gerb-ster/YUSynth-LFO/images/IMG_1308.jpeg

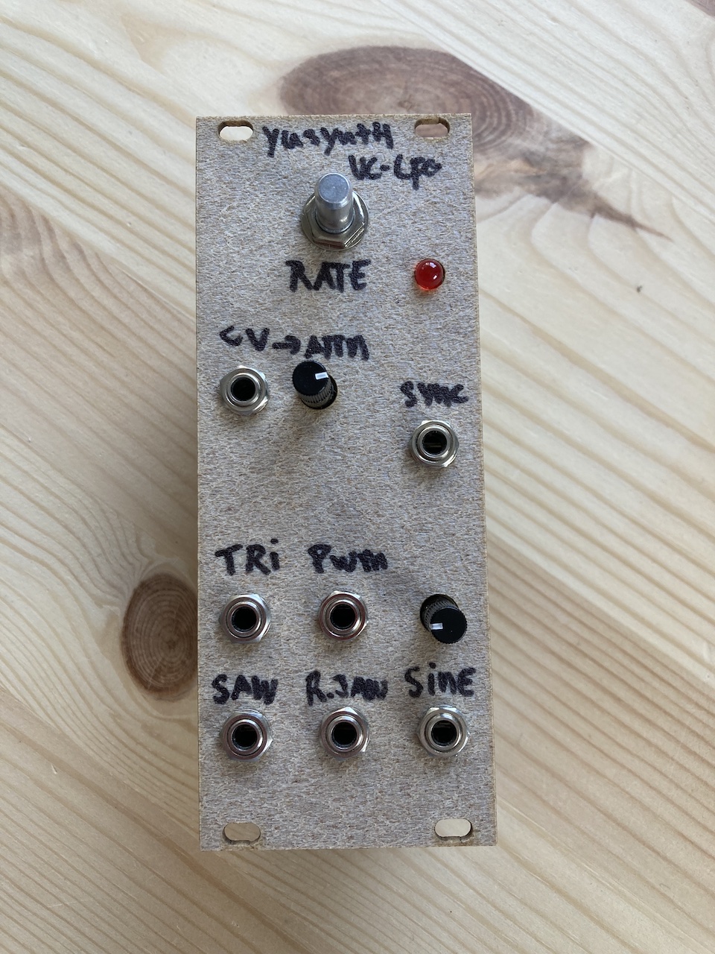
images/IMG_1308.jpeg
