gerb-ster/YUSynth-LFO/images/IMG_1309.jpeg

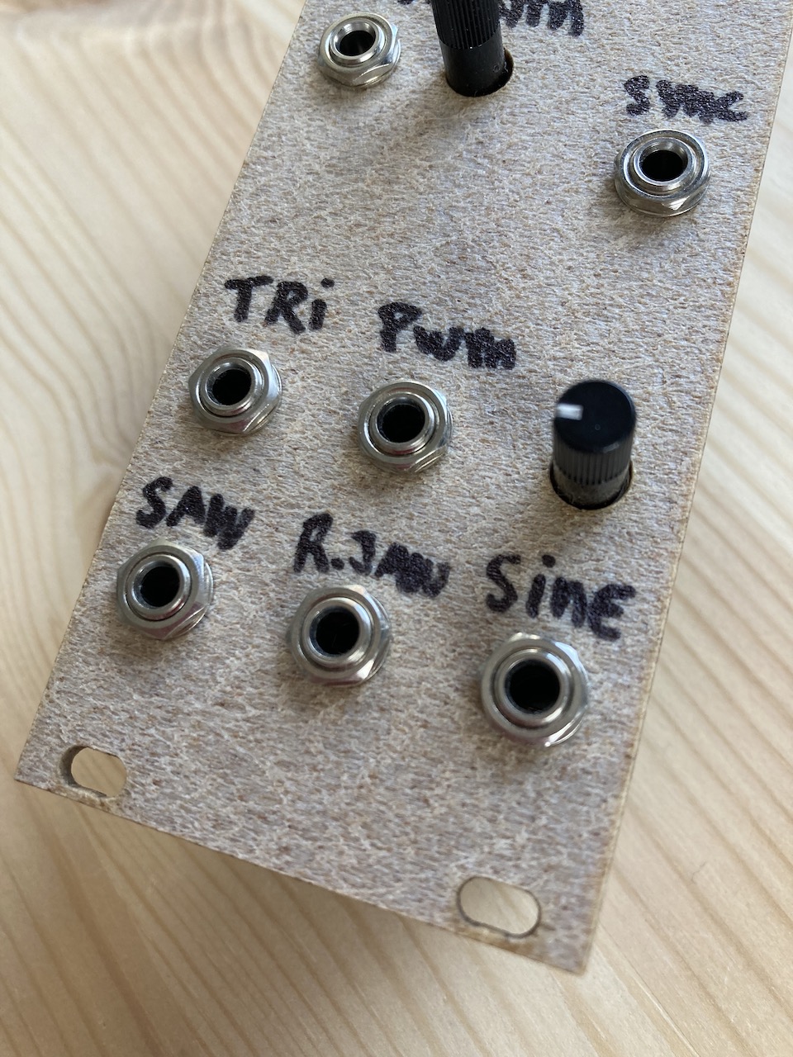
images/IMG_1309.jpeg
