gerb-ster/YUSynth-LFO/images/IMG_1310.jpeg

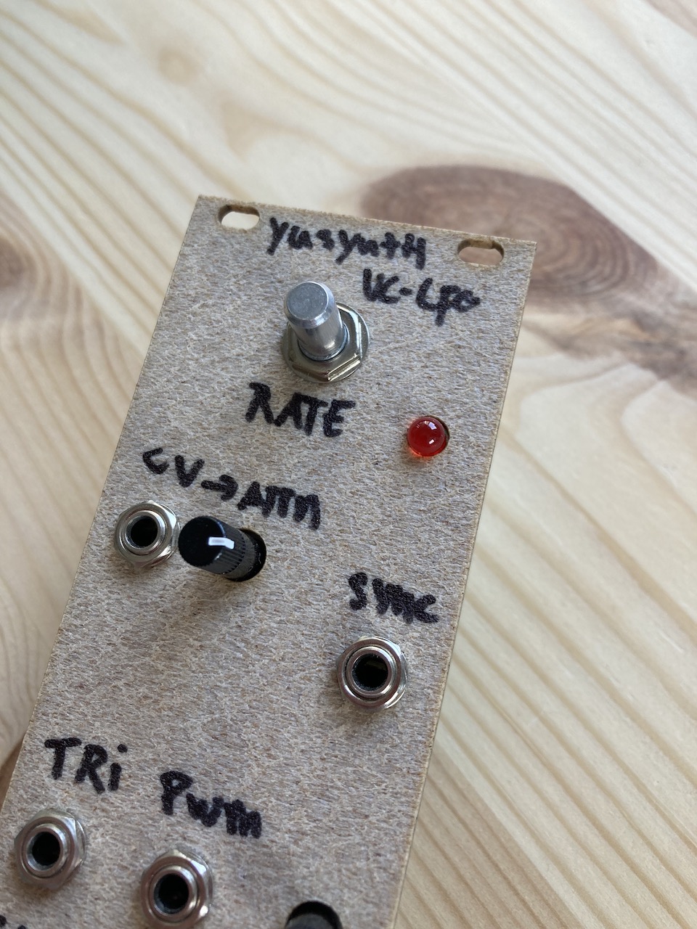
images/IMG_1310.jpeg
