gerb-ster/YUSynth-LFO/images/IMG_1311.jpeg

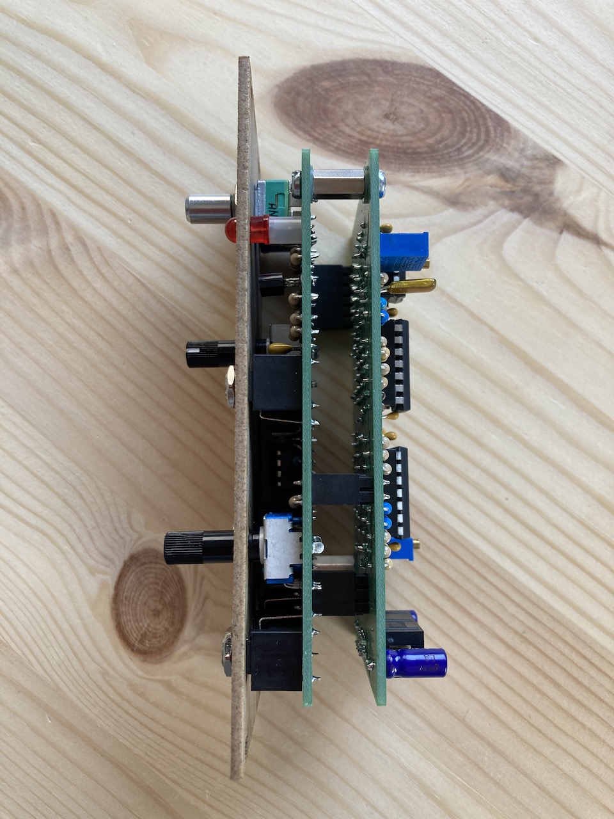
images/IMG_1311.jpeg
