gerb-ster/YUSynth-LFO/images/IMG_1313.jpeg

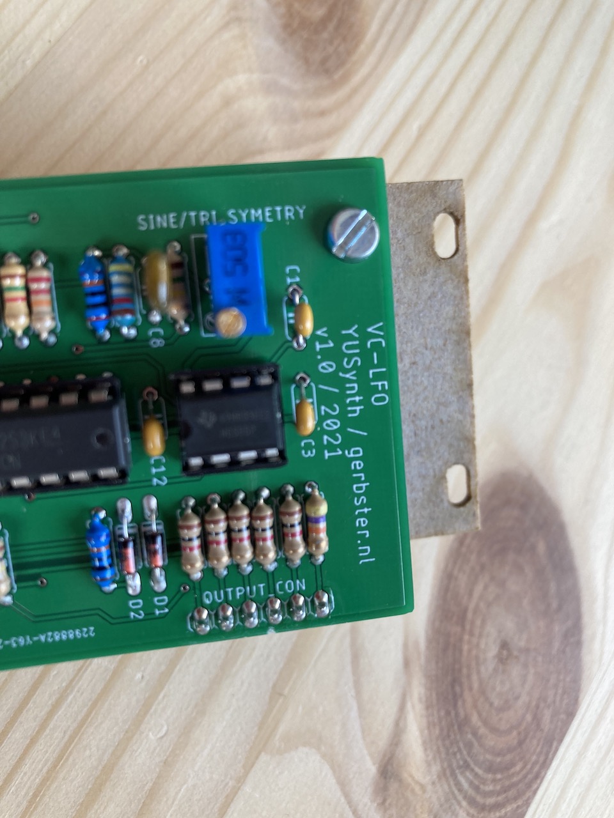
images/IMG_1313.jpeg
