gerb-ster/YUSynth-LFO/images/YUSynth-LFO-ioboard.png

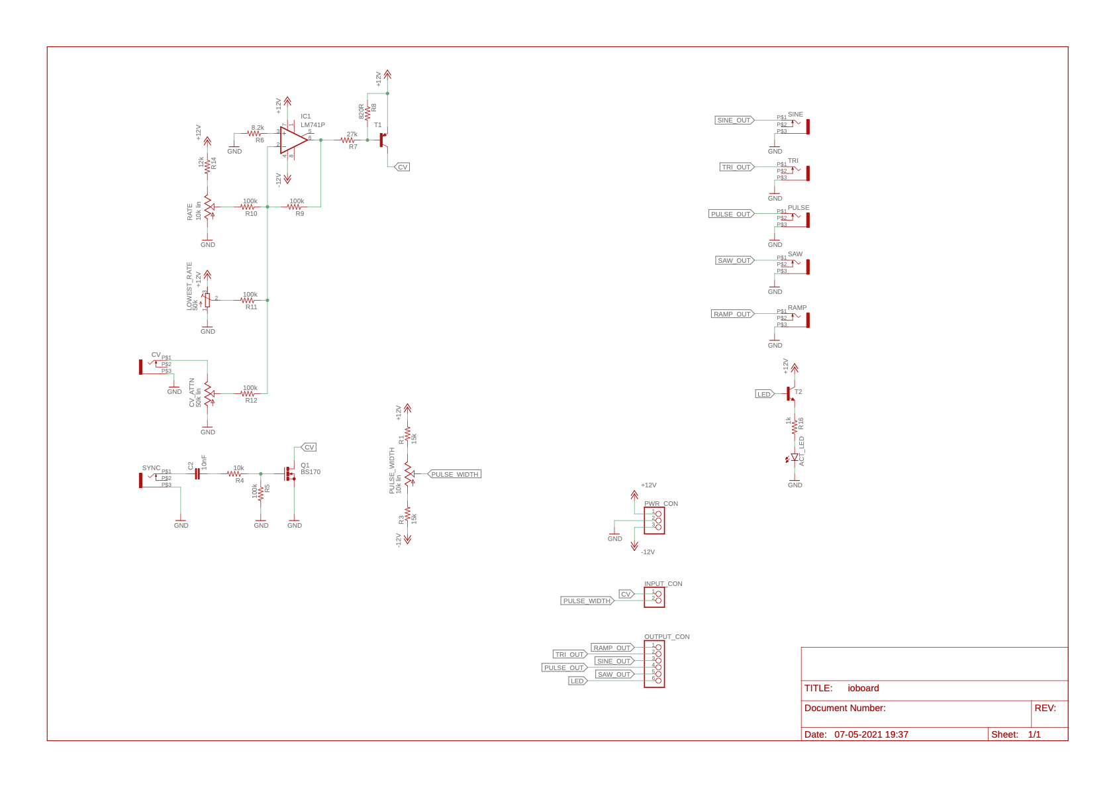
images/YUSynth-LFO-ioboard.png
