gerb-ster/YUSynth-LFO/images/YUSynth-LFO-mainboard.png

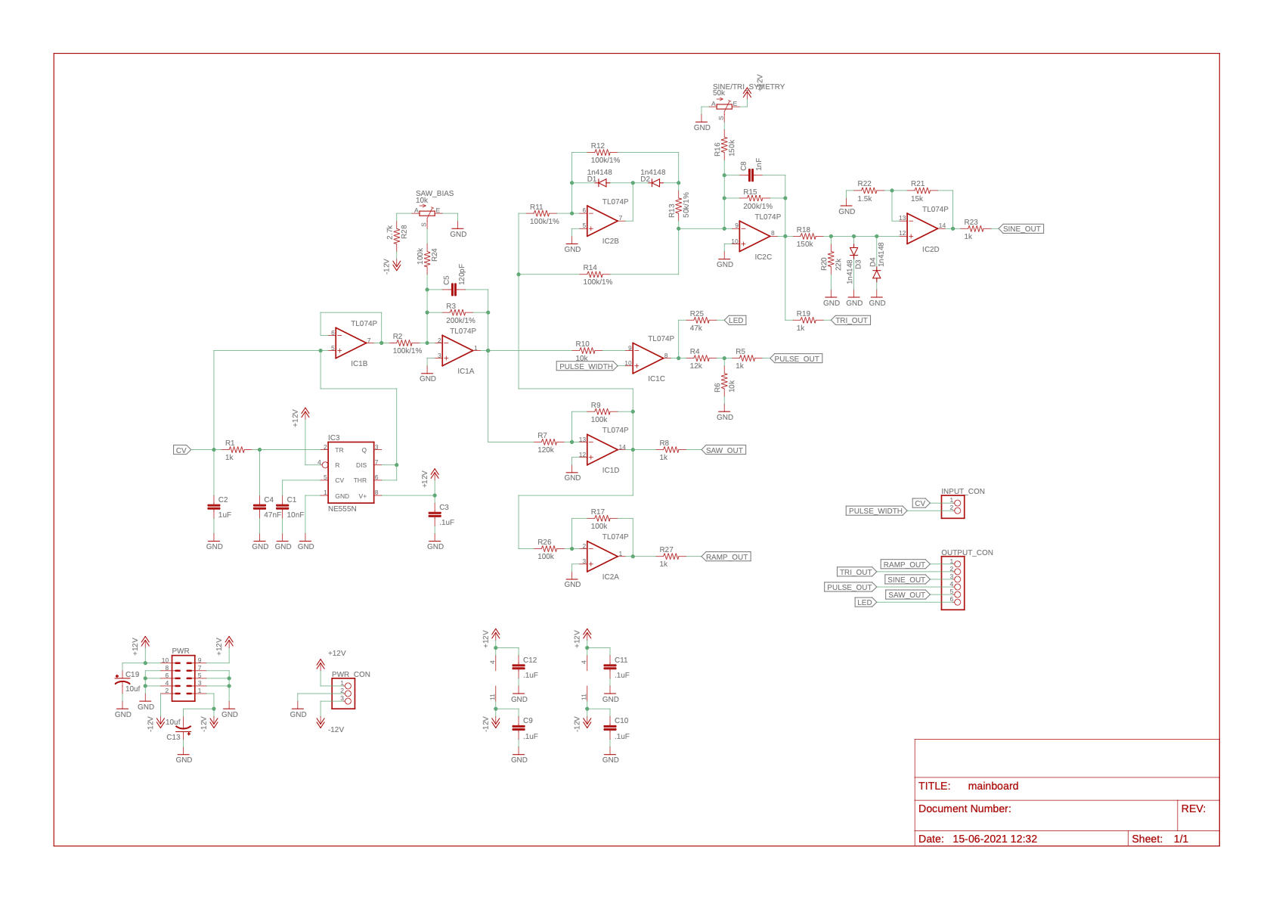
images/YUSynth-LFO-mainboard.png
